AUmakerspace510/WRO2025-FE-ALLIANCE-TECH-WIZARDS/Engineering Factor/parts_dimensions/parts_dimensions/lower_chassis/5.png

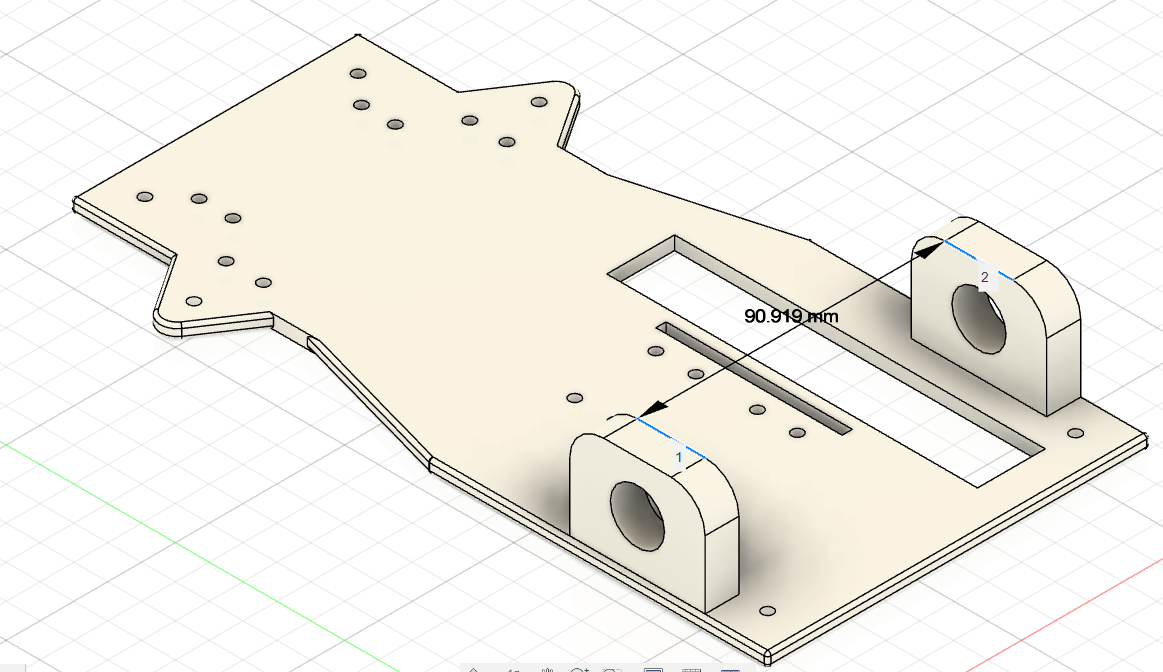
Engineering Factor/parts_dimensions/parts_dimensions/lower_chassis/5.png
