AUmakerspace510/WRO2025-FE-ALLIANCE-TECH-WIZARDS/Engineering Factor/parts_dimensions/parts_dimensions/upper_chassis/7.png

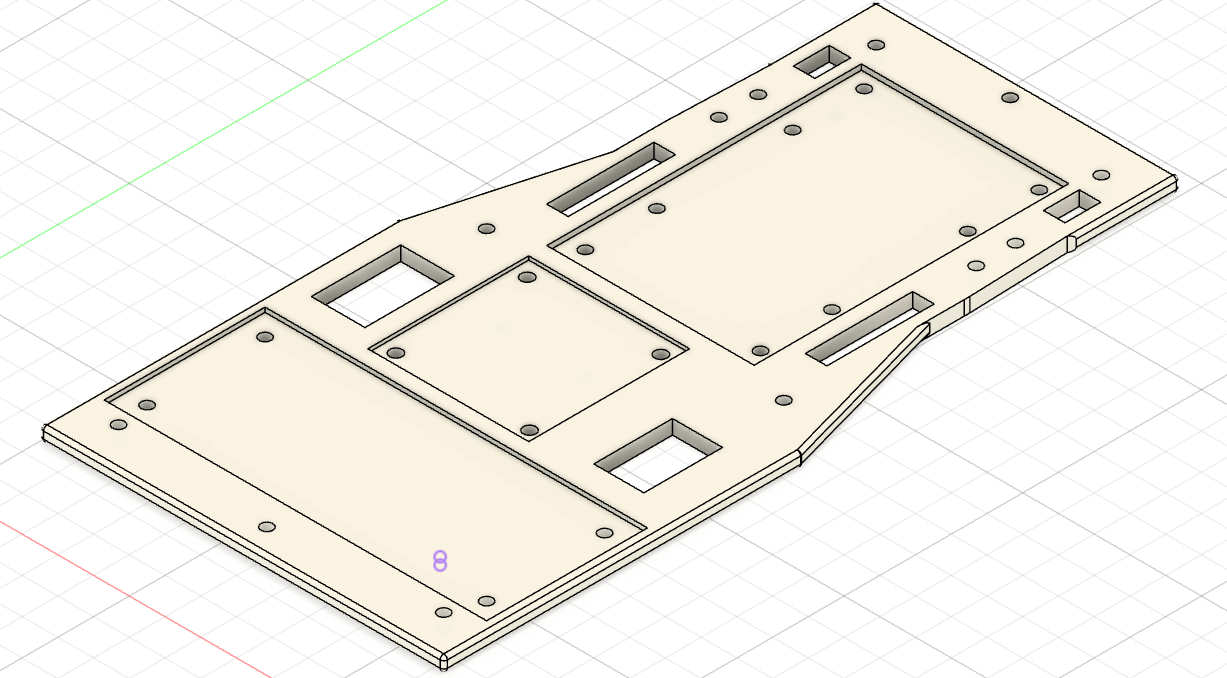
Engineering Factor/parts_dimensions/parts_dimensions/upper_chassis/7.png
