AUmakerspace510/WRO2025-FE-ALLIANCE-TECH-WIZARDS/Power and sensing/Block diagram .jpg

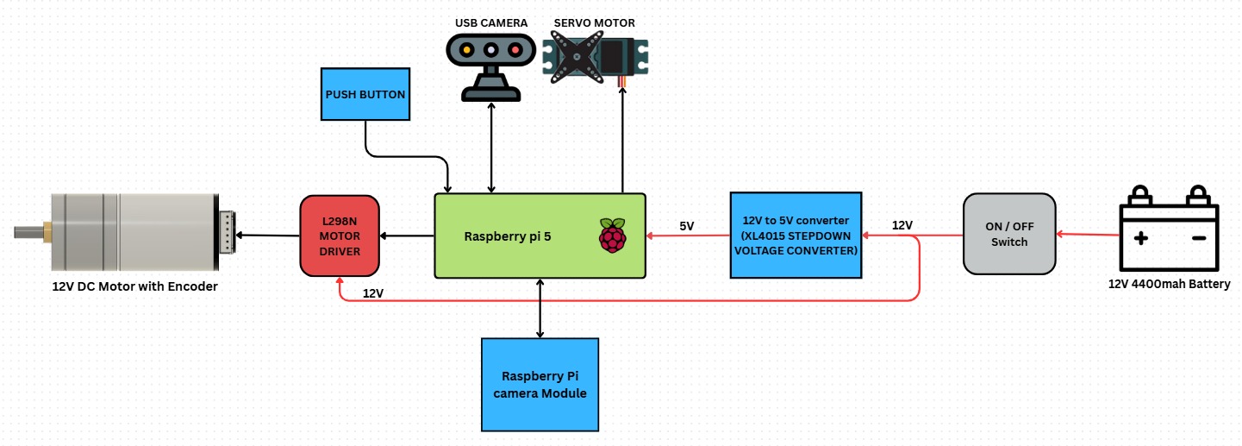
Power and sensing/Block diagram .jpg
