AUmakerspace510/WRO2025-FE-ALLIANCE-TECH-WIZARDS/Team - Vehicle Photos/Team/20250904_1138_image.png

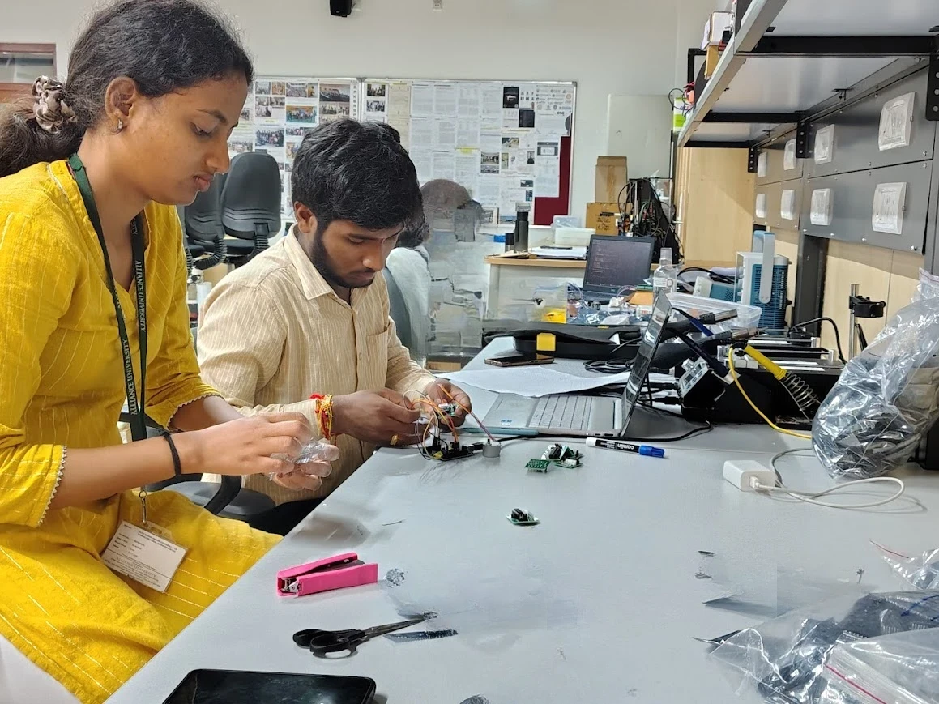
Team - Vehicle Photos/Team/20250904_1138_image.png
