AUmakerspace510/WRO2025-FE-ALLIANCE-TECH-WIZARDS/Team - Vehicle Photos/Team/_Team photo.jpg

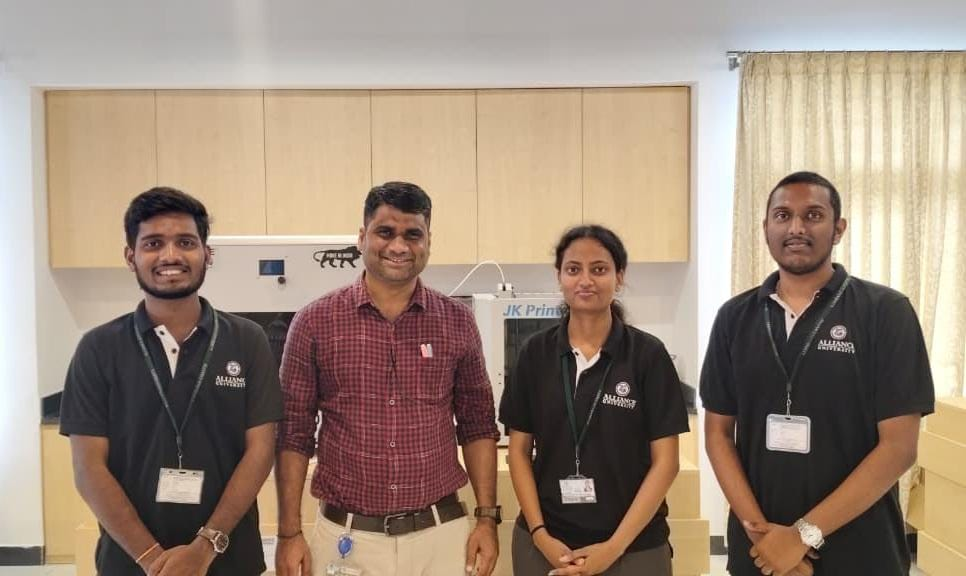
Team - Vehicle Photos/Team/_Team photo.jpg
