AUmakerspace510/WRO2025-FE-ALLIANCE-TECH-WIZARDS/Team - Vehicle Photos/Team/Funny pic.jpg

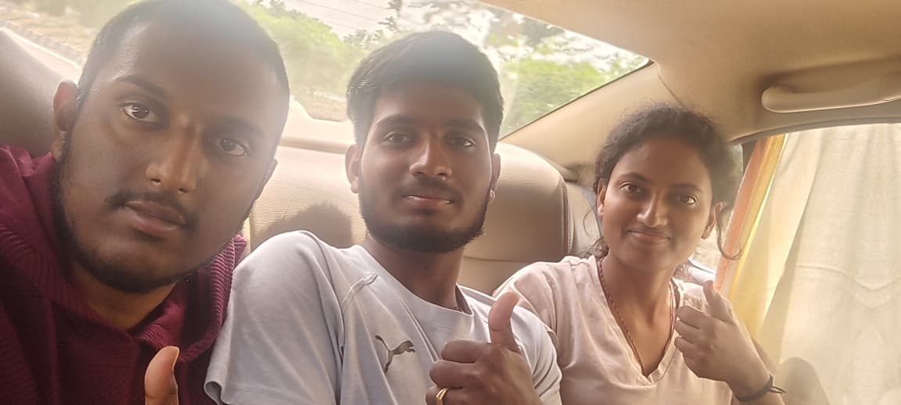
Team - Vehicle Photos/Team/Funny pic.jpg
