AUmakerspace510/WRO2025-FE-ALLIANCE-TECH-WIZARDS/Team - Vehicle Photos/Team/IMG-20250904-WA0024.jpg

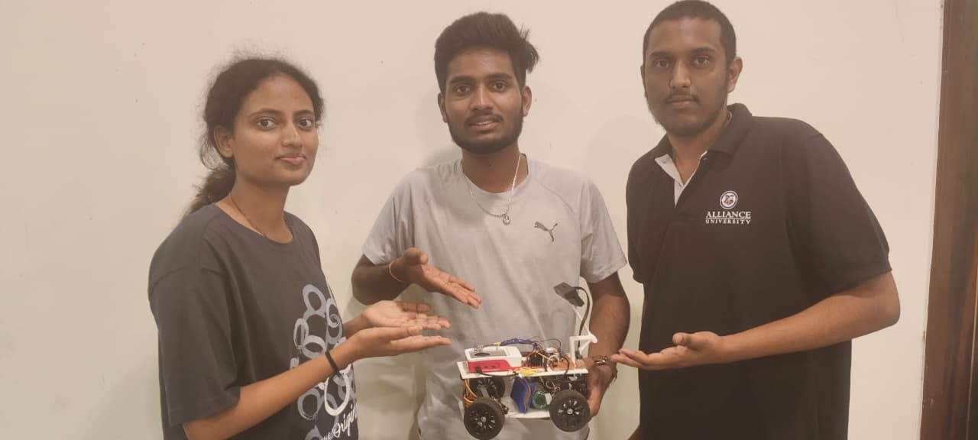
Team - Vehicle Photos/Team/IMG-20250904-WA0024.jpg
