AUmakerspace510/WRO2025-FE-ALLIANCE-TECH-WIZARDS/Team - Vehicle Photos/Team/team lead documentation.jpg

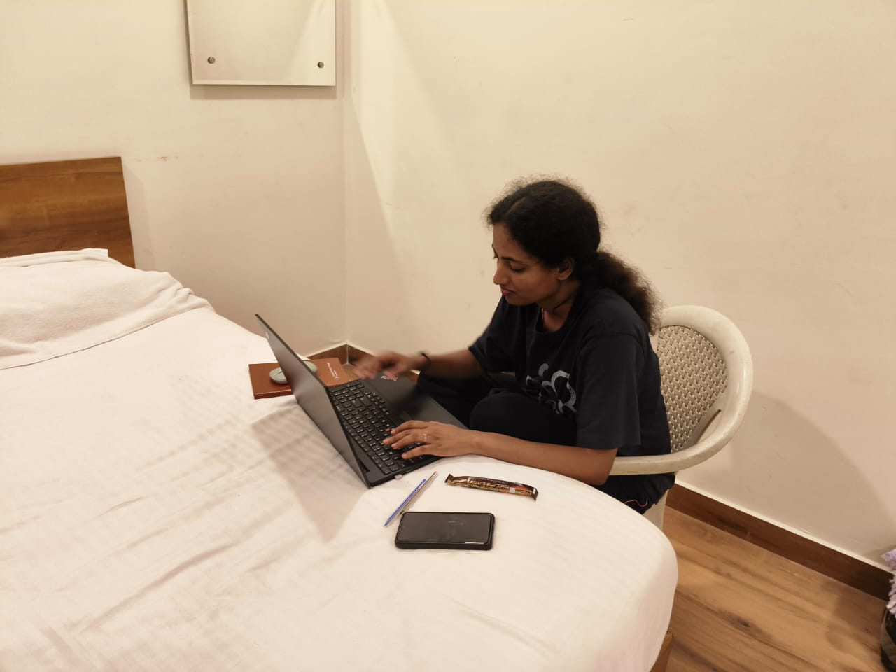
Team - Vehicle Photos/Team/team lead documentation.jpg
