AUmakerspace510/WRO2025-FE-ALLIANCE-TECH-WIZARDS/Team - Vehicle Photos/Team/team pic.jpg

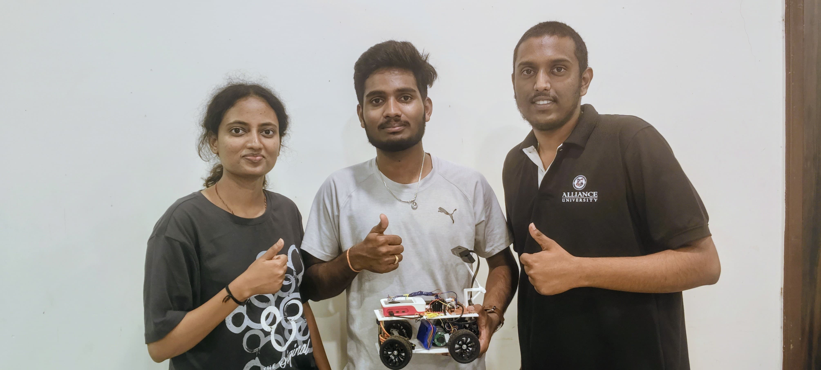
Team - Vehicle Photos/Team/team pic.jpg
