AUmakerspace510/WRO2025-FE-ALLIANCE-TECH-WIZARDS/Team - Vehicle Photos/Team/Team working 2.jpg

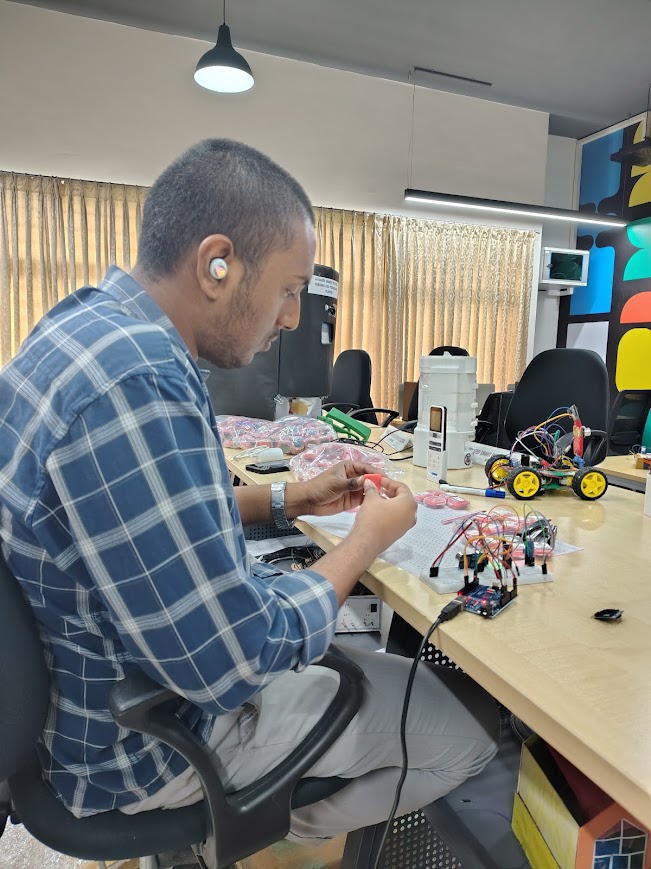
Team - Vehicle Photos/Team/Team working 2.jpg
