AUmakerspace510/WRO2025-FE-ALLIANCE-TECH-WIZARDS/Team - Vehicle Photos/Team/WhatsApp Image 2025-09-04 at 9.59.20 AM.jpeg

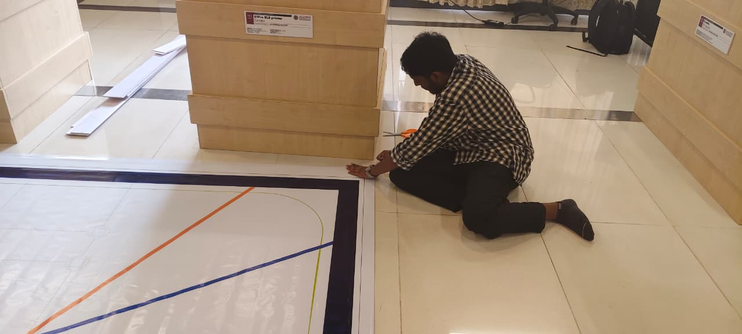
Team - Vehicle Photos/Team/WhatsApp Image 2025-09-04 at 9.59.20 AM.jpeg
