AUmakerspace510/WRO2025-FE-ALLIANCE-TECH-WIZARDS/Team - Vehicle Photos/Vehicle/Back.jpg

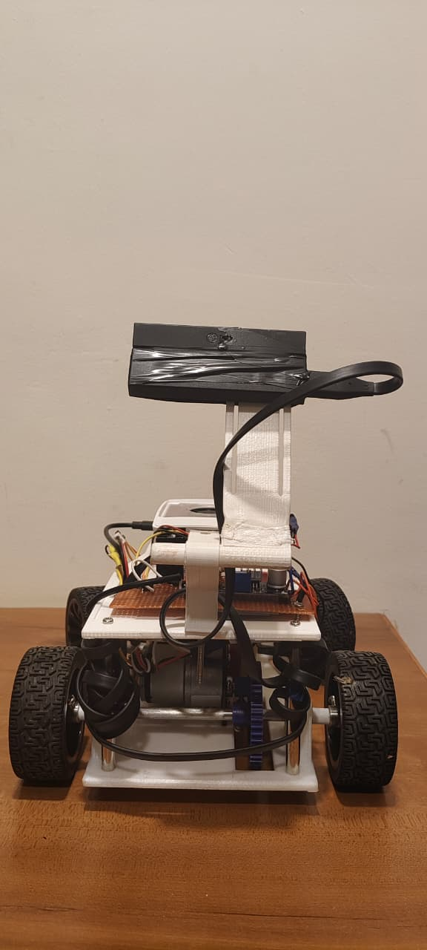
Team - Vehicle Photos/Vehicle/Back.jpg
