AUmakerspace510/WRO2025-FE-ALLIANCE-TECH-WIZARDS/Team - Vehicle Photos/Vehicle/bottom view.jpg

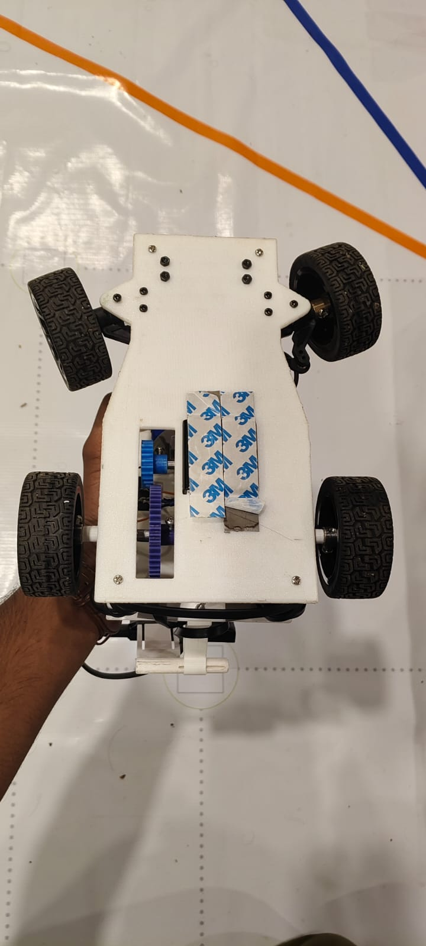
Team - Vehicle Photos/Vehicle/bottom view.jpg
