AUmakerspace510/WRO2025-FE-ALLIANCE-TECH-WIZARDS/Team - Vehicle Photos/Vehicle/IMG-20250904-WA0036.jpg

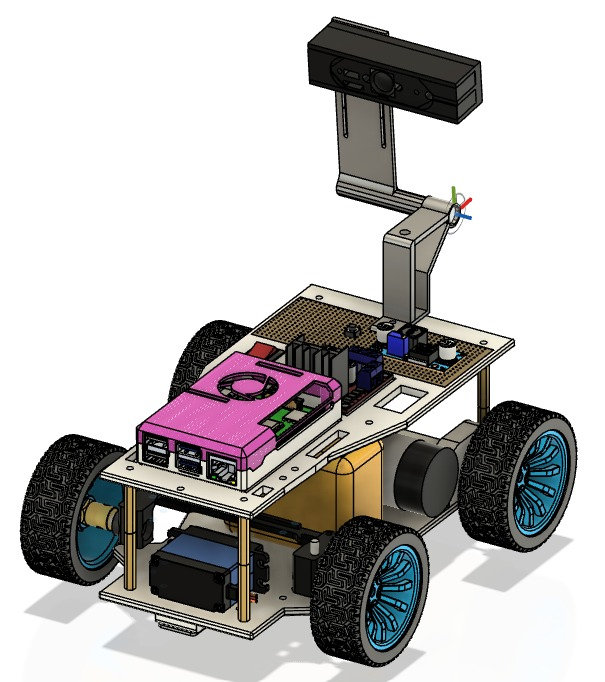
Team - Vehicle Photos/Vehicle/IMG-20250904-WA0036.jpg
