AUmakerspace510/WRO2025-FE-ALLIANCE-TECH-WIZARDS/Team - Vehicle Photos/Vehicle/IMG-20250905-WA0010.jpg

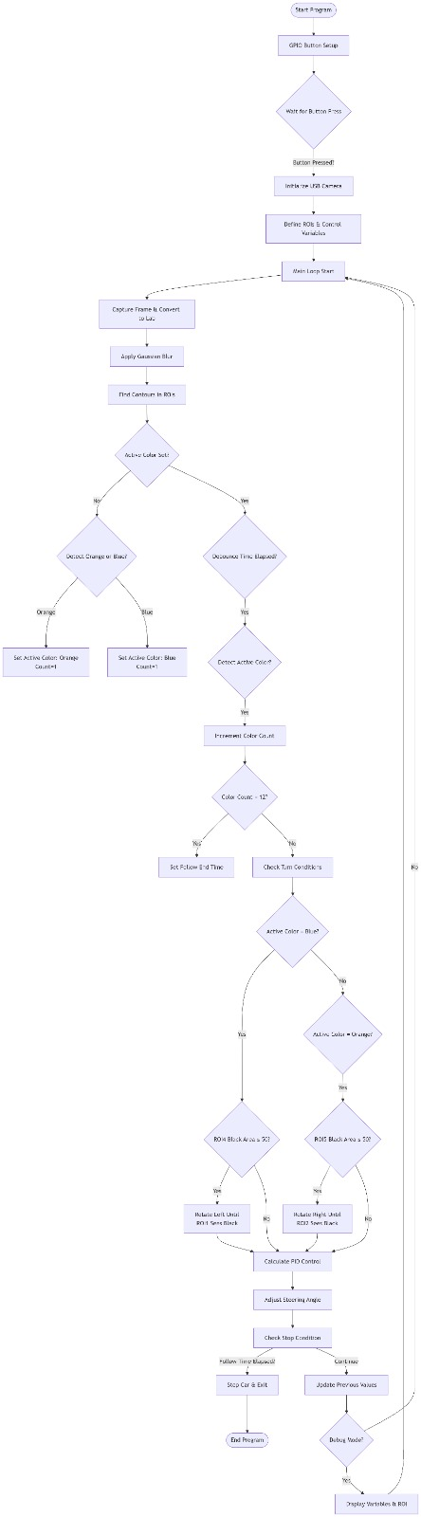
Team - Vehicle Photos/Vehicle/IMG-20250905-WA0010.jpg
