AUmakerspace510/WRO2025-FE-ALLIANCE-TECH-WIZARDS/Team - Vehicle Photos/Vehicle/IMG_20250726_090247484_HDR - Copy - Copy.jpg

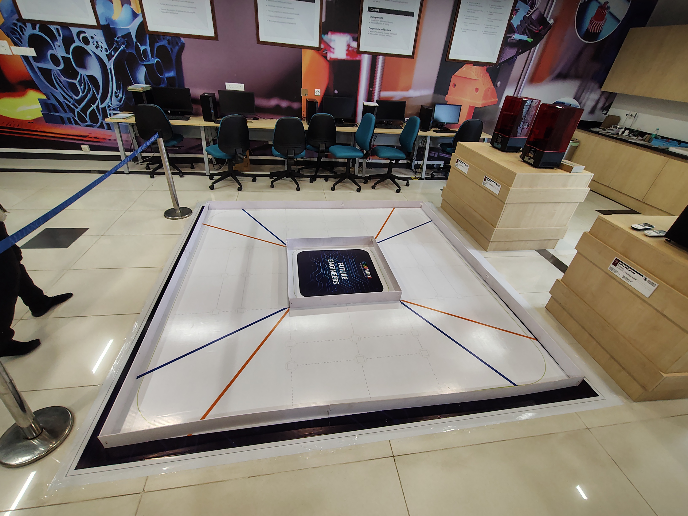
Team - Vehicle Photos/Vehicle/IMG_20250726_090247484_HDR - Copy - Copy.jpg
