AUmakerspace510/WRO2025-FE-ALLIANCE-TECH-WIZARDS/Team - Vehicle Photos/Vehicle/Isometric-1.jpg

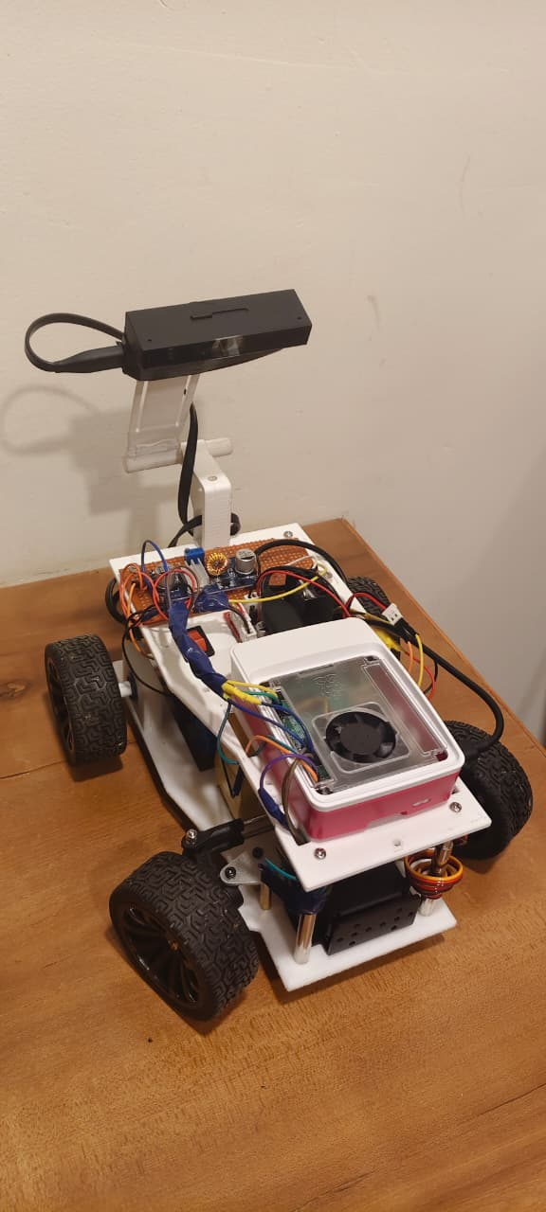
Team - Vehicle Photos/Vehicle/Isometric-1.jpg
