AUmakerspace510/WRO2025-FE-ALLIANCE-TECH-WIZARDS/Team - Vehicle Photos/Vehicle/Left.jpg

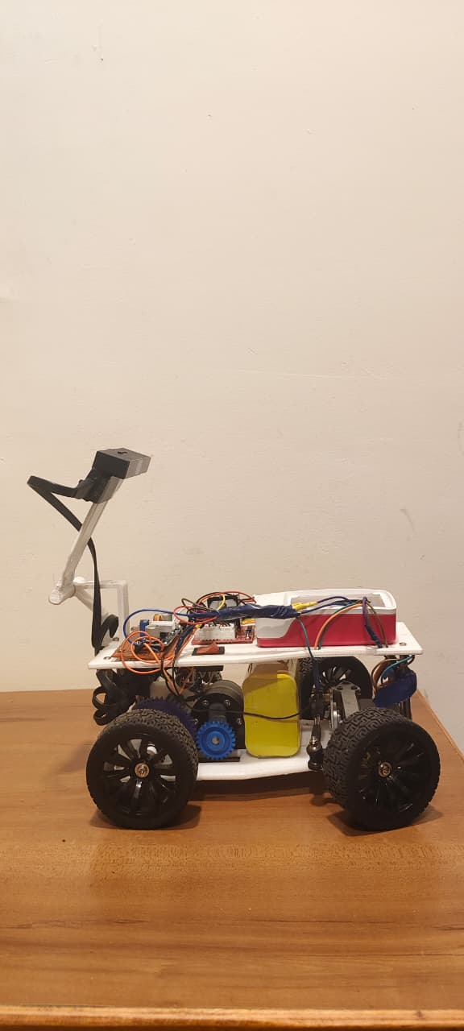
Team - Vehicle Photos/Vehicle/Left.jpg
