AUmakerspace510/WRO2025-FE-ALLIANCE-TECH-WIZARDS/Team - Vehicle Photos/Vehicle/obstacle round 2.jpg

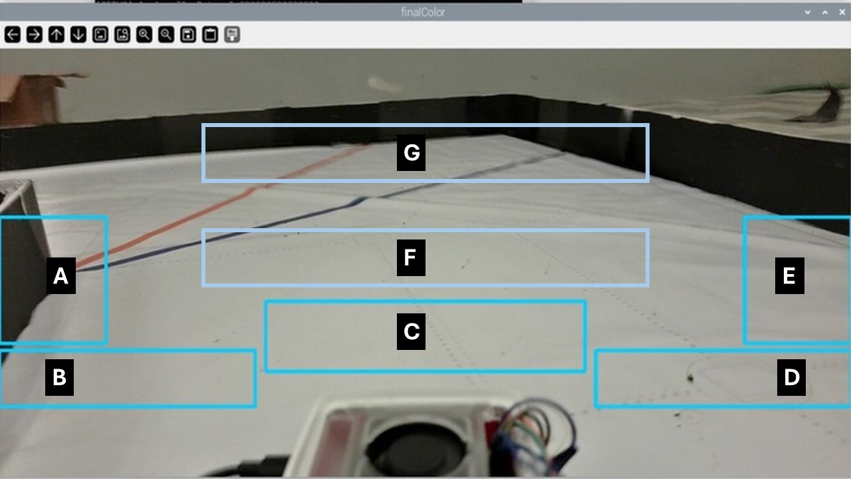
Team - Vehicle Photos/Vehicle/obstacle round 2.jpg
