AUmakerspace510/WRO2025-FE-ALLIANCE-TECH-WIZARDS/Team - Vehicle Photos/Vehicle/Team obstacles round.jpg

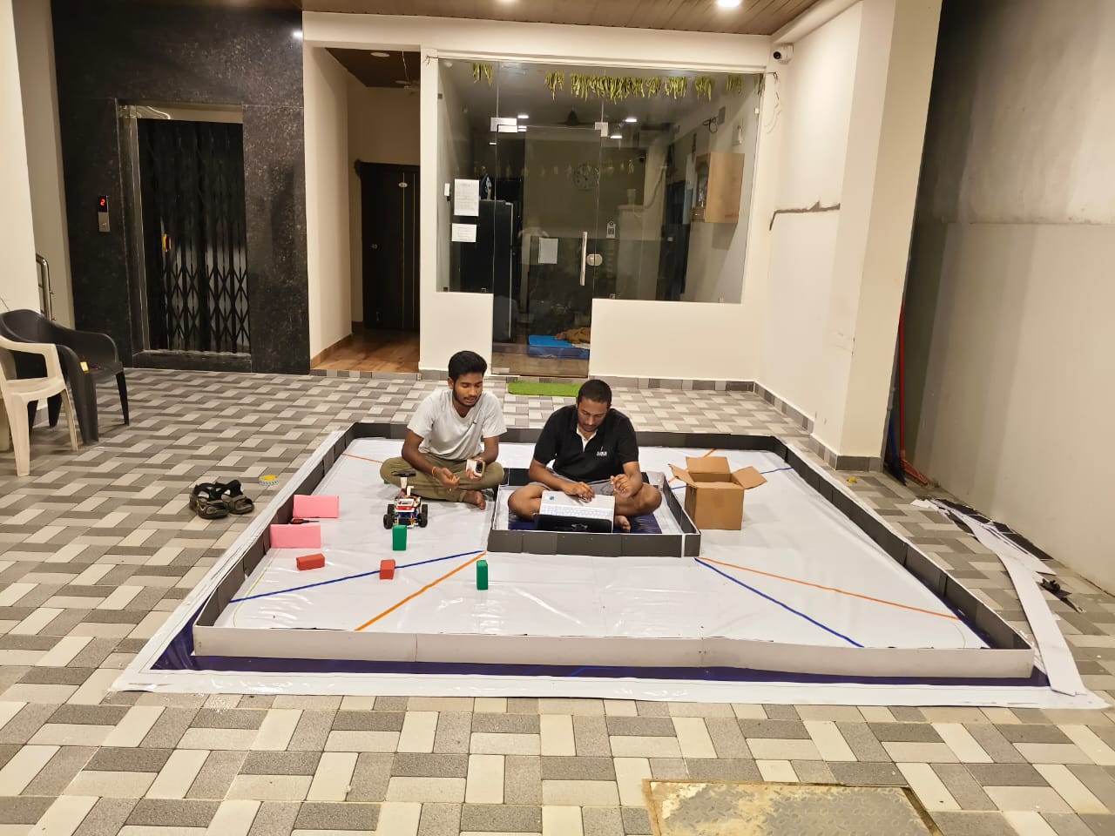
Team - Vehicle Photos/Vehicle/Team obstacles round.jpg
